romdnop/air_pressure_monitor/modelling/model.cir

[Main]
FileType=CIR
Version=12.00
Program=Micro-Cap
Component Version=10.00
Shape Version=11.00
Screen=1920,1080
MCAPVersion=12.2.0.3
Key ID=Demo
NLCnt=55
TXCnt=0

[shapedef]
Name=Capacitor
Line=0,0,22,0
Line=22,-8,22,8
Line=26,-8,26,8
Line=26,0,48,0
Current=32,12,16,12

[shapedef]
Name=Diode.root
Line=0,0,20,0
Line=28,0,48,0
Rectangle=18,-8,20,8
PolyClosed=3
PolyLine=20,0
PolyLine=28,-8
PolyLine=28,8
Current=32,16,16,16

[shapedef]
Name=DNMOS
Root="Mos2.root",0,0,0
Line=14,0,24,0
PolyClosed=3
PolyLine=17,0
PolyLine=20,-3
PolyLine=20,3

[shapedef]
Name=DPMOS
Root="Mos2.root",0,0,0
Line=14,0,24,0
PolyClosed=3
PolyLine=17,-3
PolyLine=17,3
PolyLine=20,0

[shapedef]
Name=Ground
Line=0,0,12,0
Line=12,-8,12,8
Line=18,-4,18,4
Line=24,0,24,0

[shapedef]
Name=ISOLD
Line=8,0,8,24
Line=0,24,16,24
Line=8,24,0,40
Line=8,24,16,40
Line=0,40,16,40
Line=8,42,8,64
Line=0,24,-8,32
Line=16,24,24,16
Line=16,32,56,32

[shapedef]
Name=Mos2.root
Line=0,8,10,8
Line=10,-8,10,8
Line=14,-11,14,-5
Line=14,-3,14,3
Line=14,5,14,11
Line=14,-8,24,-8
Line=14,8,24,8
Line=24,0,24,24
Line=24,-8,24,-24
Current=32,-24,32,-16
Current=32,24,32,16
Current=0,0,8,0

[shapedef]
Name=Plus.root
Line=-2,0,2,0
Line=0,-2,0,2

[shapedef]
Name=Resistor
PolyOpen=12
PolyLine=0,0
PolyLine=0,0
PolyLine=12,0
PolyLine=14,-4
PolyLine=18,4
PolyLine=22,-4
PolyLine=26,4
PolyLine=30,-4
PolyLine=34,4
PolyLine=36,0
PolyLine=48,0
PolyLine=48,0
Current=32,8,16,8

[shapedef]
Name=SPICE_V
Root="Vsource.root",0,0,0

[shapedef]
Name=Vsource.root
Line=0,0,12,0
Line=36,0,48,0
Ellipse=12,-12,36,12
FColor=None
Line=7,5,7,9
Root="Plus.root",41,7,0
Current=32,16,16,16

[shapedef]
Name=Zener
Root="Diode.root",0,0,0
Rectangle=16,-9,20,-8
Rectangle=18,8,22,9

[compdef]
Name=Resistor
Definition=Resistor
Shape=Resistor
Mask=6913
Used=169
memo=Resistor
Label Offset=18,6,8,11
PinCnt=2
Pin="Plus",6,0,-10,-4
Pin="Minus",0,0,-14,-4

[compdef]
Name=TL431
Definition=Subckt
Shape=ISOLD
Mask=4096
Used=2
memo=Adjustable Precision Shunt Regulator
Label Offset=22,39,-16,25
PinCnt=3
Pin="k",a,1,0,6,7
Pin="a",a,1,8,6,5
Pin="ref",a,7,4,-6,-2

[compdef]
Name=Ground
Definition=Ground
Shape=Ground
Mask=1793
Used=278
memo=Ground
Label Offset=0,0,0,0
PinCnt=1
Pin="PinA",0,0,-3,-7

[compdef]
Name=Voltage Source
Definition=VSpice
Shape=SPICE_V
Mask=4865
Used=39
memo=Voltage Source
Label Offset=19,13,15,13
PinCnt=2
Pin="Plus",6,0,-5,-6
Pin="Minus",0,0,-20,-6

[compdef]
Name=BZX84C4V3
Definition=Diode
Shape=Zener
Mask=4224
Used=2
memo=Zener Diode Vz=4.3V Izt=5mA Zzt=90ohm
Label Offset=18,10,12,12
PinCnt=2
Pin="Anode",6,0,-13,-8
Pin="Cathode",0,0,-27,-8
Power=0.3

[compdef]
Name=Capacitor
Definition=Capacitor
Shape=Capacitor
Mask=7425
Used=24
memo=Capacitor
Label Offset=16,12,12,12
PinCnt=2
Pin="Plus",6,0,-3,-5
Pin="Minus",0,0,-14,-5

[compdef]
Name=IRLML0100
Definition=Subckt
Shape=DNMOS
Mask=4224
Used=1
memo=N-Channel HEXFET Power MOSFET Vdss=100V Rds=220mohms
Link=http://www.irf.com/product-info/datasheets/data/irlml0100pbf.pdf
Label Offset=36,-16,-10,34
PinCnt=3
Pin="1",a,3,-3,5,7
Pin="2",a,0,1,-2,-1
Pin="3",a,3,3,5,7

[compdef]
Name=BSS84_ZX
Definition=Subckt
Shape=DPMOS
Mask=4224
Used=1
memo=P-Channel Enhancement Mode Vertical DMOS FET
Label Offset=29,-8,-8,28
PinCnt=3
Pin="4",a,0,1,-5,-3
Pin="3",a,3,-3,5,2
Pin="5",a,3,3,5,11

[Circuit]
Window Placement=2,3, -1,-1, -4,-23, 0,0,1425,582
Default Object=Color=#000080
Default Object Font=Height=-15,FStyle=0,Color=#000080,Name=Arial
Default Object Apply Border To Text=No
Default Object Apply Fill To Text=No
Default Object GridSnap=No
NodeVoltageFormat=3
CurrentFormat=3
PowerFormat=3
PathDelayFormat=3
WarningFormat=3
GridTextFormulaFormat=3
Window Placement in Transient Analysis=2,3, -1,-1, -4,-23, 22,22,1669,611
Window Placement in AC Analysis=2,3, -1,-1, -4,-23, 44,44,1691,633
SpiceType=AMBIGUOUS
Title_Block_Border=None
Title_Block=False
Show Nodes=True
Show Voltages=False
Show Current=False
Show Power=False
Show Condition=False
Show Pin Connections=False
Show Connection Warnings=False
Show Cross=False
Show Attribute Text=True
Show Grid Text=True

[Comp]
Name=Resistor
Px=488,248
Rot=3

[Attr]
ON=11,-39,PART
V=R1
Style=8192

[Attr]
ON=10,-24,RESISTANCE
V=33k
Style=8192

[Attr]
ON=0,0,PACKAGE
V

[Comp]
Name=Resistor
Px=488,360
Rot=3

[Attr]
ON=10,-39,PART
V=R2
Style=8192

[Attr]
ON=10,-23,RESISTANCE
V=4.7k
Style=8192

[Attr]
ON=0,0,PACKAGE
V

[Comp]
Name=Resistor
Px=552,240
Rot=3

[Attr]
ON=9,-39,PART
V=R3
Style=8192

[Attr]
ON=9,-23,RESISTANCE
V=10k
Style=8192

[Attr]
ON=0,0,PACKAGE
V

[Comp]
Name=TL431
Px=560,256
Rot=6

[Attr]
ON=-38,39,PART
V=X1
Style=8192

[Attr]
ON=-22,53,NAME
V=TL431

[Attr]
ON=0,0,PACKAGE
V

[Wire]
Pxs=488,248,488,288

[Wire]
Pxs=488,288,504,288

[Wire]
Pxs=488,288,488,312

[Wire]
Pxs=552,240,552,256

[Comp]
Name=Ground
Px=488,360
Rot=7

[Comp]
Name=Ground
Px=552,320
Rot=7

[Wire]
Pxs=392,120,488,120

[Comp]
Name=Resistor
Px=824,248
Rot=3

[Attr]
ON=10,-40,PART
V=R6
Style=8192

[Attr]
ON=10,-25,RESISTANCE
V=20k
Style=8192

[Attr]
ON=0,0,PACKAGE
V

[Comp]
Name=Resistor
Px=944,120
Rot=2

[Attr]
ON=12,-39,PART
V=R7
Style=8192

[Attr]
ON=12,-24,RESISTANCE
V=100
Style=8192

[Attr]
ON=0,0,PACKAGE
V

[Comp]
Name=Ground
Px=944,120
Rot=4

[Wire]
Pxs=856,120,896,120

[Comp]
Name=Voltage Source
Px=392,248
Rot=3

[Attr]
ON=-31,-27,PART
V=V1
Style=8192

[Attr]
ON=-324,-41,VALUE
V=DC 0 AC 0 0 Exp 0 100 100n 12m 14m 4m

[Attr]
ON=0,0,PACKAGE
V

[Attr]
ON=0,0,SMOOTHING
V=N
Style=256

[Attr]
ON=0,0,Saved_PulseS
V=N
Style=256

[Attr]
ON=0,0,FRACTION
V=.2
Style=256

[Attr]
ON=0,0,Saved_PulseF
V=.2
Style=256

[Attr]
ON=0,0,Saved_Pulse
V=DC 0 AC 0 0 Pulse 0 30 100n 1m 100n 10m 1u
Style=256

[Attr]
ON=0,11,Saved_Exp
V=DC 0 AC 0 0 Exp 0 100 100n 12m 14m 4m
Style=256

[Attr]
ON=0,22,Saved_None
V=DC 0 AC 1 0 
Style=256

[Attr]
ON=0,33,Saved_Define
V
Style=256

[Attr]
ON=0,44,Saved_Gaussian
V=DC 0 AC 1 0 Gaussian 1 500n 200n 1u
Style=256

[Attr]
ON=0,55,Saved_Noise
V=DC 0 AC 1 0 Noise 10n 1 0 1u
Style=256

[Attr]
ON=0,66,Saved_SFFM
V=DC 0 AC 1 0 SFFM 0 1 1e6 .5 1e7
Style=256

[Attr]
ON=0,77,Saved_PWLS
V=N
Style=256

[Attr]
ON=0,88,Saved_PWLF
V=.2
Style=256

[Attr]
ON=0,99,Saved_PWL
V=DC 0 AC 1 0 PWL 0,1 100n,2 400n,3 500n,4 600n,1 700n,2 1u,0
Style=256

[Wire]
Pxs=392,120,392,200

[Comp]
Name=Ground
Px=392,248
Rot=7

[Wire]
Pxs=488,120,488,200

[Wire]
Pxs=552,120,552,192

[Wire]
Pxs=488,120,552,120

[Wire]
Pxs=552,120,712,120

[Comp]
Name=Resistor
Px=776,128
Rot=1

[Attr]
ON=-31,23,PART
V=R12
Style=8192

[Attr]
ON=-29,8,RESISTANCE
V=100k
Style=8192

[Attr]
ON=0,0,PACKAGE
V

[Wire]
Pxs=776,120,808,120

[Wire]
Pxs=776,120,776,128

[Wire]
Pxs=776,176,776,200

[Wire]
Pxs=776,200,824,200

[Wire]
Pxs=824,144,824,200

[Wire]
Pxs=824,248,824,256

[Comp]
Name=Ground
Px=824,312
Rot=7

[Wire]
Pxs=664,296,688,296

[Wire]
Pxs=664,256,664,296

[Wire]
Pxs=552,256,664,256

[Wire]
Pxs=552,256,552,264

[Comp]
Name=Resistor
Px=712,216
Rot=3

[Attr]
ON=-32,-25,PART
V=R13
Style=8192

[Attr]
ON=-31,-39,RESISTANCE
V=15k
Style=8192

[Attr]
ON=0,0,PACKAGE
V

[Wire]
Pxs=712,120,712,168

[Wire]
Pxs=712,120,736,120

[Wire]
Pxs=712,216,712,256

[Wire]
Pxs=712,256,824,256

[Wire]
Pxs=824,256,824,264

[Comp]
Name=BZX84C4V3
Px=736,136
Rot=1

[Attr]
ON=18,10,PART
V=D1
Style=8192

[Attr]
ON=18,24,MODEL
V=BZX84C4V3

[Attr]
ON=18,38,POWER
V=0.3

[Attr]
ON=18,66,PACKAGE
V=SOT-23

[Wire]
Pxs=736,120,736,136

[Wire]
Pxs=736,120,776,120

[Wire]
Pxs=736,184,736,200

[Wire]
Pxs=736,200,776,200

[Comp]
Name=BZX84C4V3
Px=688,312
Rot=1

[Attr]
ON=18,10,PART
V=D2
Style=8192

[Attr]
ON=18,24,MODEL
V=BZX84C4V3

[Attr]
ON=18,38,POWER
V=0.3

[Attr]
ON=18,66,PACKAGE
V=SOT-23

[Comp]
Name=Capacitor
Px=752,368
Rot=5

[Attr]
ON=12,-26,PART
V=C3
Style=8192

[Attr]
ON=12,-40,CAPACITANCE
V=100n
Style=8192

[Attr]
ON=0,0,PACKAGE
V

[Comp]
Name=Ground
Px=688,360
Rot=7

[Comp]
Name=Ground
Px=752,368
Rot=7

[Wire]
Pxs=752,296,752,320

[Wire]
Pxs=752,296,800,296

[Wire]
Pxs=688,296,688,312

[Wire]
Pxs=688,296,752,296

[Comp]
Name=IRLML0100
Px=800,288

[Attr]
ON=36,-16,PART
V=X3
Style=8192

[Attr]
ON=36,-2,NAME
V=IRLML0100
Style=8192

[Attr]
ON=36,26,PACKAGE
V=MICRO3

[Comp]
Name=BSS84_ZX
Px=832,144
Rot=5

[Attr]
ON=-19,-65,PART
V=X4
Style=8192

[Attr]
ON=-19,-49,NAME
V=BSS84_ZX
Style=8192

[Attr]
ON=-29,34,PACKAGE
V=SOT-23

[Schematic]
CurrentSection 0=0
CurrentSection 1=0
CurrentSection 2=0
CurrentSection 3=0
Splitter.xs=0
Splitter.ys=0
TextQuad=4099
Scale=0.5
GridUser=10
ShapeGroups="Main","Euro","Polarity","Main1","Main11","Electrolytic","GroundArrow","DeMorgan"
CalcRMS=False
CalcAVG=False
CalcPeak=False
CalcVoltage=True
DisplayMeasure=Last
ShareScales=True

[Tools]
Pos=Top
FILESAVEASOLD=No
BOM=No
FILEPCB=No
PROBE=Yes
SELECT=Yes
PAN=Yes
COMP=Yes
TEXT=Yes
WIRE=Yes
WIRED=Yes
BUS=Yes
GRAPHIC=Yes
FLOWCHART=Yes
LINE=No
ELLIPSE=No
RECT=No
DIAM=No
ARC=No
PIE=No
TRIANGLE=No
STAR=No
LEFTBRK=No
RIGHTBRK=No
BOTHBRK=No
META=Yes
PARALLELOGRAM=No
FC_PROCESS=No
FC_ALT_PROCESS=No
FC_DECISION=No
FC_DATA=No
FC_PREDEFPROCESS=No
FC_INTERNALSTORAGE=No
FC_DOCUMENT=No
FC_MULTIDOCUMENT=No
FC_TERMINATOR=No
FC_PREPARATION=No
FC_MANUALINPUT=No
FC_MANUALOPERATION=No
FC_CONNECTOR=No
FC_OFFPAGECONNECTOR=No
FC_PUNCHCARD=No
FC_PUNCHEDTAPE=No
FC_SUMMING_JUNCTION=No
FC_OR=No
FC_COLLATE=No
FC_SORT=No
FC_EXTRACT=No
FC_MERGE=No
FC_STORED_DATA=No
FC_DELAY=No
FC_SAS=No
FC_MAGNETIC_DISK=No
FC_DAS=No
FC_DISPLAY=No
SPREAD_SHEET=Yes
POLYCLOS=No
POLYOPEN=No
FLAG=Yes
INFO=Yes
HELP=Yes
HELP_SPICE=No
LINK=Yes
CHECK=Yes
REGION_ENABLE=Yes
TITLE_BLOCK=Yes
DIGTRC=No
DIGTRC2=No
BUILD_COMMAND=Yes
DIGALL=No
GRIDTEXT=Yes
COMPTEXT=Yes
NODE=Yes
MEASURED=Yes
NODEV=Yes
CURRENT=Yes
POWER=Yes
CONDITIN=Yes
PIN=Yes
CONNWARN=Yes
CROSS=Yes
GRID=Yes
BORDER=Yes
BORDERONE=Yes
TITLE=Yes
RUBBER=Yes
PROPERTY=Yes
STEP=Yes
MIRROR=Yes
ROTATE=Yes
FLIPY=Yes
FLIPX=Yes
CIR_MAKEMACRO=No
CLEARCUTWIRE=No
CLIPBOARDCIRPAGE2BMM=No
FINDCOMP=Yes
FIND=Yes
REPEAT=No
REPLACE=No
MODEL=Yes
CIR2CKT=Yes
ATTDISP=Yes
ENABLE=Yes
DISABLE=Yes
ENABLE_WITH=Yes
TOFRONT=Yes
TOBACK=Yes
SELNEXT=Yes
PAGEADD=Yes
PAGEADDTEXT=No
ADDSECTION=No
PAGEDEL=Yes
ZOOMIN=Yes
ZOOMOUT=Yes
AUTOSCALECIR=Yes
GOTOFLAG=Yes
UPLEVEL=Yes
COLOR=Yes
FONT=Yes
STYLE=Yes
DM_LAST=No
DM_RMS=No
DM_AVG=No
DM_PEAK=No
GRID_NONE=No
GRID_NORMAL=No
GRID_BOLD_5=No
GRID_BOLD_6=No
GRID_BOLD_USER=No
GRAPH_PAPER=No
SPLITCIRTEXTH=No
SPLITCIRTEXTV=No
SPACE_SPLITTERS_EVENLY=No
NORMALCIR=No
RENAMEDEFINE=No
RENAMECMP=No
ATTALIGN=No
RESETNODEPOS=No
FIT2STANDARD=No
NODESNAP=No
MOVETEXT=No
TEXTINC=No
TOGGLETEXT=No
TOGGLEMODE=No
TOLERANCE=No
ALIGNAB=No
ALIGNLEFT=Yes
ALIGNCENTER=Yes
ALIGNRIGHT=Yes
ALIGNTOP=Yes
ALIGNMIDDLES=Yes
ALIGNBOTTOM=Yes

[Section]
Index=0
Name="model"
Type=Main
Enable=True
CurrentPage 0=0
CurrentPage 1=0
CurrentPage 2=0
CurrentPage 3=0
TabSize 0=400
TabSize 1=400
TabSize 2=400
TabSize 3=400

[Page]
Index=0
Section=0
Print=True
Enable=True
Name=Main
PrinterScale=1
Scale 0=1
Scale 1=1
Scale 2=1
SB 3=260,65
Scale 3=0.5
Px=879,184
WinBackGround Color=#FFFFFF
Select Color=#FF0000
Anchor Color=#000000
Select Box Color=#000080
Grid Text Color=Height=-12,FStyle=0,Color=#0000FF,Name=Verdana
Grid Text RTF=False
Grid Text Angle=0
Grid Text GridSnap=True
Grid Text PinIt=False
Grid Text JustifyH=Left
Grid Text JustifyV=Bottom
Grid GradientColor2=None
Grid OutlineThickness=1
Grid OutlineColor=None
Component Color=#0000FF
Attribute Text=Height=-12,FStyle=0,Color=#008000,Name=Verdana
Wire Color=#008000
Bus Color=#008000
Pin Connection=Height=-10,FStyle=0,Color=#FF0000,Name=Arial
Pin Marker Color=#008000
Node Number=Height=-11,FStyle=0,Color=#FF00FF,Name=Arial
Node Voltage Color=Height=-11,FStyle=0,Color=#000000,Name=Arial
Dynamic AC Voltage Color=#E4E4E4
Text Banner Text=Height=-15,FStyle=0,Color=#800000,Name=Arial
Title Block Background=#C0C0C0
Current=Height=-11,FStyle=0,Color=#0000FF,Name=Arial
Power/Condition=Height=-11,FStyle=0,Color=#FF0000,Name=Arial
Digital Path Color=#FF0000
Title Block Border=#000000
Disabled	Color=#C0C0C0
Search Color=#FFFF00
Grid Color=#000000
Graph Paper=#E4E4E4
Digital 0 Color=#000000
Digital R Color=#FFFF00
Digital F Color=#FFFF00
Digital 1 Color=#FF0000
Digital X Color=#C0C0C0
Digital Z Color=#808080
Block Select Color=#51F998

[Page]
Index=1
Section=0
Type=Text
Print=False
Enable=True
Name=Text
SB 0=0,2
Font=Height=-15,FStyle=0,Color=#000000,Name=Courier New
Comment Color=#008000
WinBackGround Color=#FFFFFF
Disabled	Color=#C0C0C0
KeyWord Color=#0000FF
Error	Color=#FF0000
Search Color=#FFFF00

[Page]
Index=2
Section=0
Type=Text
Print=False
Enable=True
Name=Models
SB 0=0,44
Font=Height=-15,FStyle=0,Color=#000000,Name=Courier New
Comment Color=#008000
WinBackGround Color=#FFFFFF
Disabled	Color=#C0C0C0
KeyWord Color=#0000FF
Error	Color=#FF0000
Search Color=#FFFF00

[Page]
Index=3
Section=0
Type=Info
Print=False
Enable=True
Name=Info
Font=Height=-15,FStyle=0,Color=#000000,Name=Courier New
Comment Color=#008000
WinBackGround Color=#FFFFFF
Disabled	Color=#C0C0C0
KeyWord Color=#0000FF
Error	Color=#FF0000
Search Color=#FFFF00

[Text Area]
Section=0
Page=1
Text=.OPTIONS ITL1=250
Text=.OPTIONS PIVREL=1
Text=.OPTIONS ITL4=50     

[Text Area]
Section=0
Page=2
Text=*** From file C:\MC12\library\IRPMOS.LBR
Text=*** N-Channel 500V 1.5 Ohm 4.5A
Text=.MODEL 2N6761 NMOS (CBD=397.524p CGDO=1.65276n CGSO=1.65276n GAMMA=0 GDSNOI=0
Text=+ JS=10n KP=20u L=2u LAMBDA=14.9095m NLEV=0 NSUB=0 PHI=600m RD=1.0663 RDS=2MEG
Text=+ RG=18.3254 TOX=0 TPG=1 UO=600 VTO=3.30551 W=235.519m)
Text=*** From file C:\MC12\library\HPMOS.LBR
Text=*** NMOS 5A 0.4 Ohm 100V
Text=.MODEL 2SK295 NMOS (CBD=477.65p CGDO=1.65276n CGSO=1.65276n GAMMA=0 GDSNOI=0
Text=+ JS=10n KP=20u L=2u LAMBDA=831.312f NLEV=0 NSUB=0 PHI=600m RDS=80K RG=237.587
Text=+ TOX=0 TPG=1 UO=600 VTO=3.80025 W=26.9255m)
Text=*** From file C:\MC12\library\IRPMOS.LBR
Text=*** N-Channel 600V 2.7 Ohm 3.2A
Text=.MODEL IRFBC32 NMOS (CBD=748.332p CGDO=105.87p CGSO=1.86512n GAMMA=0 GDSNOI=0
Text=+ JS=10n KP=20u L=2u LAMBDA=399.618u NLEV=0 NSUB=0 PHI=600m RD=1.59848
Text=+ RDS=2.4MEG RG=12.6657 TOX=0 TPG=1 UO=600 VTO=3.80538 W=289.347m)
Text=*** From file C:\MC12\library\SUPERTEX.LIB
Text=.MODEL 2N7002 NMOS (LEVEL=3 CGDO=6.1716E-10 CGSO=9.10E-9 DELTA=0.1
Text=+ ETA=0.0223089 KAPPA=0.0506 L=2.5E-6 LD=1.698E-9 NFS=6.6E10 NSUB=1.0E15
Text=+ RD=1.22 RS=0.0405 THETA=1.0E-5 TOX=1.0E-7 TPG=1 UO=862.425 VMAX=1.0E7
Text=+ VTO=2.00 W=0.5E-2 XJ=6.4666E-7)
Text=*** From file C:\MC12\library\SUPERTEX.LIB
Text=.MODEL 2N7000 NMOS (LEVEL=3 CGDO=3.1716E-9 CGSO=9.09E-9 DELTA=0.1 ETA=0.0223089
Text=+ KAPPA=0.0506 L=2.5E-6 LD=1.698E-9 NFS=6.6E10 NSUB=1.0E15 RD=0.239 RS=0.205
Text=+ THETA=1.0E-5 TOX=1.0E-7 TPG=1 UO=862.425 VMAX=1.0E7 VTO=1.000 W=0.8E-2
Text=+ XJ=6.4666E-7)
Text=*** From file C:\MC12\library\IRPMOS.LBR
Text=*** PMOS 11A 0.3 Ohm 100V
Text=.MODEL 2N6804 PMOS (CBD=1.13578n CGDO=1.7627n CGSO=5.27853n GAMMA=0 GDSNOI=0
Text=+ JS=10n KP=20u L=2u LAMBDA=27.4551f NLEV=0 NSUB=0 PHI=600m RD=111.44m
Text=+ RDS=400MEG RG=39.8973 TOX=0 TPG=1 UO=600 VTO=-3.01473 W=137.406m)
Text=*** From file C:\MC12\library\SUPERTEX.LIB
Text=.MODEL TP2502 PMOS (LEVEL=3 CGDO=3.172E-10 CGSO=2.750E-9 DELTA=1.0 ETA=0.053089
Text=+ KAPPA=1.20 KP=4.3E-6 L=2.0E-6 LD=1.698E-9 NFS=6.6E10 NSUB=1.0E15 RD=0.25
Text=+ RS=0.03 THETA=1.0E-5 TOX=725E-10 TPG=1 UO=862.425 VMAX=5.0E6 VTO=-2.0 W=60E-3
Text=+ XJ=6.4666E-7)
Text=*** From file C:\MC12\library\MC_MOSFET.LIB
Text=.MODEL TP2504 PMOS (LEVEL=3 CGDO=3.172E-10 CGSO=2.750E-9 DELTA=1.0 ETA=0.053089
Text=+ KAPPA=1.20 KP=4.3E-6 L=2.0E-6 LD=1.698E-9 NFS=6.6E10 NSUB=1.0E15 RD=0.25
Text=+ RS=0.03 THETA=1.0E-5 TOX=725E-10 TPG=1 UO=862.425 VMAX=5.0E6 VTO=-2.0 W=60E-3
Text=+ XJ=6.4666E-7)
Text=*** From file C:\MC12\library\SUPERTEX.LIB
Text=.MODEL TP2104 PMOS (LEVEL=3 CGDO=6.1716E-10 CGSO=9.10E-9 DELTA=0.1 ETA=0.12098
Text=+ KAPPA=0.0411 L=2.5E-6 LD=1.6980E-9 NFS=3.384E11 NSUB=5.0E14 RD=1.91 RS=0.73
Text=+ THETA=4.063E-5 TOX=1.0E-7 TPG=-1 UO=865.45 VMAX=3.0E6 VTO=-2.10 W=0.5E-2
Text=+ XJ=6.5E-7)

[InfoPage]
InfoPage=True
Warnings=True
System=True
Defines=True
Array=True
Model=True
Measure=True
MacroSubckt=True
NotUsed=True
ComponentCounts=True
VariablizePaths=False
DontShowPaths=False
SimulationLog=True

[Transient]
WinID=1
Window Placement=2,3, -1,-1, -4,-23, 22,22,1669,611
Font=Height=-19,FStyle=0,Color=#0000FF,Name=Arial
WinBackGround Color=#FFFFFF
Select Color=#FF0000
Anchor Color=#000000
Select Box Color=#000080
Title
AutoTitle=Yes
Grid Color=#808080
Grid Weight=1
Grid Pattern=Dot6
Tracker Foreground=Height=-15,FStyle=0,Color=#000000,Name=Arial
Tracker Background=#FFFF00
Baseline color=#0000FF
BaseLine Weight=1
CurveFit color=#FF0000
CurveFit Weight=2
CurveFit Pattern=Dash
Static Grids=False
PlusMark=False
MinorLog25=Off
LabelMinor=Off
DataPoints=False
Token=False
Ruler=False
XAxisGrids=True
YAxisGrids=True
MinorLogGrids=True
BaseLine=False
AlignZ=True
Align Cursors=True
TagFormatX=3
TagFormatY=3
FormulaFormat=2
EndMode=SCALE
Graph Background=#FFFFFF
Tracker Intercept=False
Tracker Mouse=True
Tracker Cursor=True
Tracker Cursor BranchInfo=False
Horizontal Cursor=False
Same Y Scales=Yes
Enable X Scaling=True
Enable Y Scaling=True
Keep X Scales The Same=True
Number of Grids X=5
Number of Grids Y=5
Cursor Select Color Primary=#C0C0C0
Cursor Select Color Secondary=#FF0000
Data Point Labels Color Fore=Height=-15,FStyle=0,Color=#000000,Name=Arial
Data Point Labels Color Back=#FFFF00
OperPoint=True
OperPointOnly=False
AutoScaleRanges=True
FixedTimeStep=False
DoPSS=False
PSS_Periods="1"
PSS_Iterations="5"
PSS_Error="1u"
PSS_ShowPlots=True
FFT_NPts="8192"
FFT_IncludeDCHarmonic=False
FFT_AutoScale_Harmonics="10"
PrinterAutoTile=No
PrinterBlackBorder=No
MonMaxShow=2
MonPageWidth=66
MonPlotWidth=21
MonExprXWidth=142
MonExprYWidth=376
MonRangeXWidth=90
MonRangeYWidth=90
AnimateWait=None
AnimateWaitTime=500
AnimatePressAfter=0
Save_For_Future=No
Reduce_Display=1
Reduce_Save=1
Reduce_ThrowDataOut=0
Num Out Header Left
Num Out Header Center="$MC\n$user\n$company\n$Analysis of $name\n$date $time"
Num Out Header Right
Num Out Delimiter=32
Num Out Write=True
Num Out Write Main Header=True
Num Out Write Limits=True
Num Out Write Branch Header=True
Num Out Write Models=False
Num Out Write Zero Models=True
Num Out Write Undefined Models=True
Num Out Write Operating Point=True
Num Out Write Measurement Values=True
Num Out Write Tolerance Detail=True
Num Out Write Values=True
Num Out Write Waveform Header=True
Num Out Allow Dup Y Expr=False
Num Out Low="TSTART"
Num Out High="TMAX"
Num Out Font=Height=-15,FStyle=0,Color=#000000,Name=Courier New
Num Out Format=3
Num Out HideNonSelected=False
Num Out UseActualDataPoints=False
AutoSaveWave=False
Wave Format=16E
State Variables Format=5E
Print Individual Pages=False

[Tools]
Pos=Top
SELECT=Yes
PAN=Yes
GRAPHIC=Yes
LINE=No
ELLIPSE=No
RECT=No
DIAM=No
ARC=No
PIE=No
TRIANGLE=No
STAR=No
LEFTBRK=No
RIGHTBRK=No
BOTHBRK=No
META=Yes
PARALLELOGRAM=No
POLYCLOS=No
POLYOPEN=No
SCALE=Yes
CURSOR=Yes
MEASUREH=Yes
MEASUREV=Yes
TAG=Yes
PTAG=Yes
TEXT=Yes
PROPERTY=Yes
START=Yes
STOP=Yes
PAUSE=Yes
RESUME=No
DATAPTS=Yes
TOKENS=Yes
RULER=Yes
PLUS=Yes
XAXIS=Yes
YAXIS=Yes
MINORLOG=Yes
LOG25=Yes
BASELINE=Yes
HORIZCUR=Yes
GOTOX=Yes
GOTOY=Yes
GOTOPERF=Yes
GOTOBRNC=Yes
CLEAR_ACCUMULATED=Yes
PDELETE_ALL_PLOTS=Yes
NEXT=Yes
NEXTIN=Yes
PEAK=Yes
VALLEY=Yes
HIGH=Yes
LOW=Yes
INFLECTN=Yes
GHIGH=Yes
GLOW=Yes
BOTTOM=Yes
TOP=Yes
WAVEFORMBUFFER=Yes
AOUTPUT=Yes
PKEY=Yes
ENXSCALE=Yes
ENYSCALE=Yes
ZOOMIN=Yes
ZOOMOUT=Yes
AUTOSCALE=Yes
RESTORESCALE=No
COLOR=Yes
FONT=Yes
STYLE=Yes
SELNEXT=Yes
NORMALIZE=No
NORMALIZE_MIN=No
NORMALIZE_MAX=No
ADD_TAG_LEFT=No
ADD_TAG_RIGHT=No
ADD_HORZ_TAG=No
ADD_VERT_TAG=No
ALIGN_CURSORS=No
ALIGN_CURSORSZ=No
CURSORTOCLIPBOARD=No
TRACKER_CURSOR=No
TRACKER_CURSOR_BRANCHINFO=No
TRACKER_INTERCEPT=No
TRACKER_MOUSE=No
TOFRONT=Yes
TOBACK=Yes
SPLITCIRTEXTH=No
SPLITCIRTEXTV=No
SPACE_SPLITTERS_EVENLY=No
NORMALCIR=No
LABEL_WAVEFORM=No
LABEL_DATA_POINTS=No
WFB_ADD_TO_LIMITS=No
ENVELOPE=No
SAMEYSCALES=No
KEEPXSCALESTHESAME=No
CURVEFIT=No
ADD_MARKER=No
SHOWWATCH=No
BP=No
TOGGLEMODE=No
REMOVEALLTEXT=No
AUTOSCALEX=No
LABELALLMINOR=No
ALIGNLEFT=Yes
ALIGNCENTER=Yes
ALIGNRIGHT=Yes
ALIGNTOP=Yes
ALIGNMIDDLES=Yes
ALIGNBOTTOM=Yes

[APage]
Analysis=Transient
Name="MAIN"

[AC]
WinID=2
Window Placement=2,3, -1,-1, -4,-23, 44,44,1691,633
Font=Height=-19,FStyle=0,Color=#0000FF,Name=Arial
WinBackGround Color=#FFFFFF
Select Color=#FF0000
Anchor Color=#000000
Select Box Color=#000080
Title
AutoTitle=Yes
Grid Color=#808080
Grid Weight=1
Grid Pattern=Dot6
Tracker Foreground=Height=-15,FStyle=0,Color=#000000,Name=Arial
Tracker Background=#FFFF00
Baseline color=#0000FF
BaseLine Weight=1
CurveFit color=#FF0000
CurveFit Weight=2
CurveFit Pattern=Dash
Static Grids=False
PlusMark=False
MinorLog25=Off
LabelMinor=Off
DataPoints=False
Token=False
Ruler=False
XAxisGrids=True
YAxisGrids=True
MinorLogGrids=True
BaseLine=False
AlignZ=True
Align Cursors=True
TagFormatX=3
TagFormatY=3
FormulaFormat=2
EndMode=SCALE
Graph Background=#FFFFFF
Tracker Intercept=False
Tracker Mouse=True
Tracker Cursor=True
Tracker Cursor BranchInfo=False
Horizontal Cursor=False
Same Y Scales=Yes
Enable X Scaling=True
Enable Y Scaling=True
Keep X Scales The Same=True
Number of Grids X=5
Number of Grids Y=5
Cursor Select Color Primary=#C0C0C0
Cursor Select Color Secondary=#FF0000
Data Point Labels Color Fore=Height=-15,FStyle=0,Color=#000000,Name=Arial
Data Point Labels Color Back=#FFFF00
OperPoint=True
AutoScaleRanges=True
FFT_NPts="8192"
FFT_IncludeDCHarmonic=False
FFT_AutoScale_Harmonics="10"
PrinterAutoTile=No
PrinterBlackBorder=No
MonMaxShow=3
MonPageWidth=66
MonPlotWidth=21
MonExprXWidth=142
MonExprYWidth=269
MonRangeXWidth=90
MonRangeYWidth=90
AnimateWait=None
AnimateWaitTime=500
AnimatePressAfter=0
Save_For_Future=No
Reduce_Display=1
Reduce_Save=1
Reduce_ThrowDataOut=0
Num Out Header Left
Num Out Header Center="$MC\n$user\n$company\n$Analysis of $name\n$date $time"
Num Out Header Right
Num Out Delimiter=32
Num Out Write=True
Num Out Write Main Header=True
Num Out Write Limits=True
Num Out Write Branch Header=True
Num Out Write Models=False
Num Out Write Zero Models=True
Num Out Write Undefined Models=True
Num Out Write Operating Point=True
Num Out Write Measurement Values=True
Num Out Write Tolerance Detail=True
Num Out Write Noise=True
Num Out Write Values=True
Num Out Write Waveform Header=True
Num Out Allow Dup Y Expr=False
Num Out Low="FMIN"
Num Out High="FMAX"
Num Out Font=Height=-15,FStyle=0,Color=#000000,Name=Courier New
Num Out Format=3
Num Out HideNonSelected=False
Num Out UseActualDataPoints=False
AutoSaveWave=False
Wave Format=16E
State Variables Format=5E
Print Individual Pages=False

[Tools]
Pos=Top
SELECT=Yes
PAN=Yes
GRAPHIC=Yes
LINE=No
ELLIPSE=No
RECT=No
DIAM=No
ARC=No
PIE=No
TRIANGLE=No
STAR=No
LEFTBRK=No
RIGHTBRK=No
BOTHBRK=No
META=Yes
PARALLELOGRAM=No
POLYCLOS=No
POLYOPEN=No
SCALE=Yes
CURSOR=Yes
MEASUREH=Yes
MEASUREV=Yes
TAG=Yes
PTAG=Yes
TEXT=Yes
PROPERTY=Yes
START=Yes
STOP=Yes
PAUSE=Yes
RESUME=No
DATAPTS=Yes
TOKENS=Yes
RULER=Yes
PLUS=Yes
XAXIS=Yes
YAXIS=Yes
MINORLOG=Yes
LOG25=Yes
BASELINE=Yes
HORIZCUR=Yes
GOTOX=Yes
GOTOY=Yes
GOTOPERF=Yes
GOTOBRNC=Yes
CLEAR_ACCUMULATED=Yes
PDELETE_ALL_PLOTS=Yes
NEXT=Yes
NEXTIN=Yes
PEAK=Yes
VALLEY=Yes
HIGH=Yes
LOW=Yes
INFLECTN=Yes
GHIGH=Yes
GLOW=Yes
BOTTOM=Yes
TOP=Yes
WAVEFORMBUFFER=Yes
AOUTPUT=Yes
PKEY=Yes
ENXSCALE=Yes
ENYSCALE=Yes
ZOOMIN=Yes
ZOOMOUT=Yes
AUTOSCALE=Yes
RESTORESCALE=No
COLOR=Yes
FONT=Yes
STYLE=Yes
SELNEXT=Yes
NORMALIZE=No
NORMALIZE_MIN=No
NORMALIZE_MAX=No
ADD_TAG_LEFT=No
ADD_TAG_RIGHT=No
ADD_HORZ_TAG=No
ADD_VERT_TAG=No
ALIGN_CURSORS=No
ALIGN_CURSORSZ=No
CURSORTOCLIPBOARD=No
TRACKER_CURSOR=No
TRACKER_CURSOR_BRANCHINFO=No
TRACKER_INTERCEPT=No
TRACKER_MOUSE=No
TOFRONT=Yes
TOBACK=Yes
SPLITCIRTEXTH=No
SPLITCIRTEXTV=No
SPACE_SPLITTERS_EVENLY=No
NORMALCIR=No
LABEL_WAVEFORM=No
LABEL_DATA_POINTS=No
WFB_ADD_TO_LIMITS=No
ENVELOPE=No
SAMEYSCALES=No
KEEPXSCALESTHESAME=No
CURVEFIT=No
ADD_MARKER=No
SHOWWATCH=No
BP=No
TOGGLEMODE=No
REMOVEALLTEXT=No
AUTOSCALEX=No
LABELALLMINOR=No
ALIGNLEFT=Yes
ALIGNCENTER=Yes
ALIGNRIGHT=Yes
ALIGNTOP=Yes
ALIGNMIDDLES=Yes
ALIGNBOTTOM=Yes

[APage]
Analysis=AC
Name="MAIN"

[Monte Carlo Options]
Analysis=Transient
Status=Off
Zero Tolerance=False
Eliminate Outliers=False
Distribution=Normal
Number of Runs=10
Seed=0

[Monte Carlo Options]
Analysis=AC
Status=Off
Zero Tolerance=False
Eliminate Outliers=False
Distribution=Normal
Number of Runs=10
Seed=0

[Limits]
Analysis=Transient
TMax=20m
TStart=0
TStep=0
NPts=51
Temp=27
RetraceRuns=1
StateVar=Zero
RunOption=Normal
Temperature Type=Linear
Accumulate Plots=False
IgnoreExprErrors=False

[WaveForm]
Analysis=Transient
Plt=1
AliasID=1
XExp=T
YExp=v(1)
XRng=0.02
YRng=100,-25
Options=LINEARX,LINEARY
Range Grid X=0.004
Range Grid Y=25
Enable=Enable
Line Color=#0000FF
Text Color=#0000FF
Rainbow=False
VFmtX=3
VFmtY=3
ScaleFactorX="None"
ScaleFactorY="None"
ScaleUnitsX="Auto"
ScaleUnitsY="Auto"
SFmtX=2
SFmtY=2
NOFmtX=3E
NOFmtY=3E

[WaveForm]
Analysis=Transient
Plt=1
AliasID=4
XExp=T
YExp=v(6)
XRng=0.02
YRng=100,-25
Options=LINEARX,LINEARY
Range Grid X=0.004
Range Grid Y=25
Enable=Enable
Line Color=#FF00FF
Text Color=#FF00FF
Rainbow=False
VFmtX=3
VFmtY=3
ScaleFactorX="None"
ScaleFactorY="None"
ScaleUnitsX="Auto"
ScaleUnitsY="Auto"
SFmtX=2
SFmtY=2
NOFmtX=3E
NOFmtY=3E

[Limits]
Analysis=AC
FRange=1E8,1Meg
NPts=1001
Temp=27
MaxChng=5
NInput=NONE
NOutput=2
Sweep type=Log
StateVar=Zero
RunOption=Normal
Temperature Type=Linear
Accumulate Plots=False
IgnoreExprErrors=False
FirstValueDisplay=Mag
SecondValueDisplay=PhaseDeg
DisplayValuesInProbe=DC

[WaveForm]
Analysis=AC
Plt=1
AliasID=1
XExp=F
YExp=dB(v(1))
XRng=1e+8,1e+6
YRng=0,-2000
Options=LINEARY
Range Grid X=1.98e+7
Range Grid Y=400
Enable=Enable
Line Color=#0000FF
Text Color=#0000FF
Rainbow=False
VFmtX=3
VFmtY=3
ScaleFactorX="None"
ScaleFactorY="None"
ScaleUnitsX="Auto"
ScaleUnitsY="Auto"
SFmtX=2
SFmtY=2
NOFmtX=3E
NOFmtY=3E

[WaveForm]
Analysis=AC
Plt=2
AliasID=2
XExp=F
YExp=ph(v(1))
XRng=1e+8,1e+6
YRng=1,-1
Options=LINEARY
Range Grid X=1.98e+7
Range Grid Y=0.5
Enable=Enable
Line Color=#FF0000
Text Color=#FF0000
Rainbow=False
VFmtX=3
VFmtY=3
ScaleFactorX="None"
ScaleFactorY="None"
ScaleUnitsX="Auto"
ScaleUnitsY="Auto"
SFmtX=2
SFmtY=2
NOFmtX=3E
NOFmtY=3E

[WaveForm]
Analysis=AC
AliasID=-1
Options=LINEARY
Enable=Enable
Line Color=#008000
Text Color=#008000
Rainbow=False
VFmtX=3
VFmtY=3
ScaleFactorX="None"
ScaleFactorY="None"
ScaleUnitsX="Auto"
ScaleUnitsY="Auto"
SFmtX=2
SFmtY=2
NOFmtX=3E
NOFmtY=3E

[Limits]
Analysis=DynamicAC
FirstValueDisplay=Mag
SecondValueDisplay=PhaseDeg
PlaceText=True

[Limits]
Analysis=DynamicDC
PlaceText=True

[Pane]
Analysis=Transient
CurrentPage 0="MAIN"

[Pane]
Analysis=AC
CurrentPage 0="MAIN"

[Pane]
Analysis=DC

[Pane]
Analysis=HmDistortion

[Pane]
Analysis=ImDistortion

[Pane]
Analysis=Stability

[Watch]
Analysis=Transient
Format=3
ExprPercentWidth=80

[Watch]
Analysis=AC
Format=3
ExprPercentWidth=80

[WCTolerance]
Var Width=100
Nominal Width=72
Tol Width=152
Tol Name=Drift
Col Width Neq=50
Col Width Pos=50
Col Width Rnd=50

[WCFiles]
UseFile=<Library>Standard.tlib
AVAILABLE_FILE=<Library>Standard.tlib

[OPMethods]
Analysis=Transient
Standard Newton-Raphson=0,0
Source Stepping=0,0
Diagonal Gmin Stepping=0,0
Junction Gmin Stepping=0,0
Pseudo Transient=0,0

[OPMethods]
Analysis=AC
Standard Newton-Raphson=0,0
Source Stepping=0,0
Diagonal Gmin Stepping=0,0
Junction Gmin Stepping=0,0
Pseudo Transient=0,0

[OPMethods]
Analysis=DC
Standard Newton-Raphson=0,0
Source Stepping=0,0
Diagonal Gmin Stepping=0,0
Junction Gmin Stepping=0,0
Pseudo Transient=0,0

[OPMethods]
Analysis=HmDistortion
Standard Newton-Raphson=0,0
Source Stepping=0,0
Diagonal Gmin Stepping=0,0
Junction Gmin Stepping=0,0
Pseudo Transient=0,0

[OPMethods]
Analysis=ImDistortion
Standard Newton-Raphson=0,0
Source Stepping=0,0
Diagonal Gmin Stepping=0,0
Junction Gmin Stepping=0,0
Pseudo Transient=0,0

[OPMethods]
Analysis=Stability
Standard Newton-Raphson=0,0
Source Stepping=0,0
Diagonal Gmin Stepping=0,0
Junction Gmin Stepping=0,0
Pseudo Transient=0,0

[OPMethods]
Analysis=DynamicAC
Standard Newton-Raphson=0,0
Source Stepping=0,0
Diagonal Gmin Stepping=0,0
Junction Gmin Stepping=0,0
Pseudo Transient=0,0

[OPMethods]
Analysis=DynamicDC
Standard Newton-Raphson=0,0
Source Stepping=0,0
Diagonal Gmin Stepping=0,0
Junction Gmin Stepping=0,0
Pseudo Transient=0,0
