romdnop/air_pressure_monitor/modelling/power_protection.asc

C1: cap; 0.1µ
C2: cap; 0.1µ
R1: res; 68k
R2: res; 4k7
R3: res; 100k
R4: res; 40k
R5: res; 100k
R6: res; 10k
R7: res; 15k
U1: TL431
U2: 2N7002
U4: BZT52C6V8
U5: BZT52C6V8
U6: NDS0605
V1: voltage-; PULSE(0 100 0.005 0.001 0.001 0.01)
Named nets: 0
.tran 0.02
